Anvently/portable-bike-perception-rpi-ros2/core/src/cyclosafe/cyclosafe/src/ACamera.py

# Created on Tue Aug 05 2025
# Updated on Tue Aug 05 2025
#
#  This file is part of Cyclosafe
# Copyright (c) 2025 Nicolas Pirard @Anvently
#
# This software is governed by the CeCILL license under French law and
# abiding by the rules of distribution of free software. You can use,
# modify and/or redistribute the software under the terms of the CeCILL
# license as circulated by CEA, CNRS and INRIA at:
# https://cecill.info/licences/Licence_CeCILL-B_V1-en.html


from rclpy.node import Node, ParameterDescriptor
from rcl_interfaces.msg import ParameterDescriptor
from sensor_msgs.msg import CompressedImage, Image
from collections import deque
from abc import abstractmethod
from cyclosafe_interfaces.srv import SaveImages
from enum import IntEnum
import os
import cv2
from rclpy.time import Time, S_TO_NS
from typing import Any

MS_TO_NS = (1000 * 1000)

IMAGES_PATH = os.getenv("HOME") + "/data/images/"

class SaveFilesResult(IntEnum):
	SUCCESS = 0
	PARTIAL_SUCCESS = 1
	FAILURE = 2

class AImagePublisher(Node):

	def __init__(self):
		super().__init__('camera_publisher')

		try:

			self.declare_parameter('queue_size', 0, ParameterDescriptor(description="Max number of images stored in memory."))
			self.declare_parameter('resolution', [800, 600], ParameterDescriptor(description="Image resolution: [width, height]"))
			self.declare_parameter('interval', 0.5, ParameterDescriptor(description="Interval during each image"))
			self.declare_parameter('compression', 95, ParameterDescriptor(description="Compression level [0-100]"))
			self.declare_parameter('preview', False, ParameterDescriptor(description="Enable/Disable preview. Only before start"))
			self.declare_parameter('start_time', 0.0, ParameterDescriptor(description="Time to be used as the beginning of the simulation. Float value of seconds since epoch."))
			self.declare_parameter('no_compression', False, ParameterDescriptor(description="Disable jpeg compression. Use Image instead of CompressedImage."))
			self.update_parameters()

			self.preview = self.get_parameter('preview').get_parameter_value().bool_value
			self.no_compression = self.get_parameter('no_compression').get_parameter_value().bool_value

			self.start_time = Time(seconds=self.get_parameter('start_time').get_parameter_value().double_value, clock_type=self.get_clock().clock_type)

			self.img_queue = deque(maxlen=self.queue_size)
			self.count = 0

			self.init_camera()
			
			if self.no_compression == False:
				self.pub = self.create_publisher(CompressedImage, 'images/compressed', 10)
			else:
				self.pub = self.create_publisher(Image, 'images', 10)
			self.save_service = self.create_service(SaveImages, 'save_images', self.save_files)
			self.timer = self.create_timer(self.interval, self.routine)
		
		except RuntimeError as e:
			self.get_logger().error(f'Failed to init camera: {str(e)}')
			raise e
	
		self.get_logger().info('Camera publisher node started')

	@abstractmethod
	def init_camera(self):
		pass

	@abstractmethod
	def capture(self):
		pass

	def	get_current_timestamp(self) -> int:
		"""Return the current time in ms from the beginning of the simulation"""
		now: Time = self.get_clock().now()
		return (int((now - self.start_time).nanoseconds / MS_TO_NS))

	def save_files(self, request: SaveImages.Request, response : SaveImages.Response) -> SaveImages.Response:
		try:
			if (self.queue_size < 1 or len(self.img_queue) == 0):
				raise Exception("no image available")
			now = self.get_current_timestamp()
			delta: int = now - self.img_queue[0][0]
			if (delta >= request.time):
				response.result = SaveFilesResult.SUCCESS
			else:
				response.result = SaveFilesResult.PARTIAL_SUCCESS

			for i in range(0, len(self.img_queue)):
				(img_timestamp, compressed_img) = self.img_queue[i]
				if (now - img_timestamp > request.time):
					continue
				path: str = f"{request.path}/{img_timestamp}.jpg"
				if (os.path.isfile(path)):
					continue
				# Écrire directement l'image compressée
				with open(path, 'wb') as f:
					f.write(compressed_img.tobytes())
	
		except Exception as e:
			self.get_logger().error(f"SaveFiles service: Failed to save images: {str(e)}")
			response.result = SaveFilesResult.FAILURE
		return response

	def compress(self, image_array) -> Any:
		# try:
		# 	bgr_img = cv2.cvtColor(image_array, cv2.COLOR_RGB2BGR)
		# except cv2.error as e:
		# 	self.get_logger().error(f"Color conversion failed: {str(e)}")
		# 	return
		
		# Encoder l'image en JPEG avec le niveau de compression défini
		encode_param = [int(cv2.IMWRITE_JPEG_QUALITY), self.compression]
		
		# Vérification avant encodage
		if image_array is None or image_array.size == 0:
			self.get_logger().warn("Image is empty after color conversion!")
			return
		
		_, compressed_img = cv2.imencode('.jpg', image_array, encode_param)
		return (compressed_img)

	def publish(self, timestamp, img_data):
		if self.no_compression == False:
			msg = CompressedImage()
			msg.format = 'jpeg'
			msg.data = bytes(img_data.tobytes())
		else:
			msg = Image()
			msg.height = self.resolution[1]
			msg.width = self.resolution[0]
			msg.encoding = 'bgr8'  # ou 'rgb8' selon votre format
			msg.step = self.resolution[0] * 3  # 3 bytes par pixel pour BGR/RGB
			msg.is_bigendian = False
			msg.data = bytes(img_data.flatten().tobytes())
		
		msg.header.stamp = self.get_clock().now().to_msg()
		self.pub.publish(msg)

	def update_parameters(self):
		self.compression = self.get_parameter('compression').get_parameter_value().integer_value
		# self.queue_size = self.get_parameter('queue_size').get_parameter_value().integer_value
		queue_size = self.get_parameter('queue_size').get_parameter_value().integer_value
		if (hasattr(self, 'img_queue') and queue_size != self.queue_size):
			self.img_queue = deque(maxlen=self.queue_size)
		self.queue_size = queue_size
		self.interval = self.get_parameter('interval').get_parameter_value().double_value
		if (hasattr(self, 'timer')):
			self.timer.timer_period_ns = self.interval * 1000 * 1000 * 1000
		self.resolution = self.get_parameter('resolution').get_parameter_value().integer_array_value

	def routine(self):
		try:
			self.update_parameters()
			image_array = self.capture()
			timestamp = self.get_current_timestamp()
			
			if self.no_compression == False:
				image_compressed = self.compress(image_array)
				self.publish(timestamp, image_compressed)
				queue_data = image_compressed
			else:
				# Pour les images non compressées, stockez l'array original
				self.publish(timestamp, image_array)
				queue_data = image_array
				
			if (self.queue_size > 0):
				self.img_queue.append((timestamp, queue_data))
			self.count += 1
		except Exception as e:
			self.get_logger().error(f"Failed to capture image: {str(e)}")
